MoSPDude/ZXTeensyIF1/ZXTeensyIF1/if1-2_rom.h

// if1-2.rom
// Sinclair-Interface-1-v2
#define BUILTIN_ROM_IF1_SIZE 8192
{
    0xE1, 0xFD, 0x36, 0x7C, 0x00, 0xC3, 0x00, 0x07,
    0x2A, 0x5D, 0x5C, 0xE1, 0xE5, 0xC3, 0x9A, 0x00,
    0x22, 0xBA, 0x5C, 0xE1, 0xD5, 0x18, 0x6A, 0xFF,
    0xFD, 0xCB, 0x01, 0x7E, 0xC9, 0xFF, 0xFF, 0xFF,
    0xDF, 0x28, 0x45, 0x18, 0x15, 0xFF, 0xFF, 0xFF,
    0xFD, 0xCB, 0x02, 0x9E, 0x18, 0x12, 0xFF, 0xFF,
    0xC3, 0xF7, 0x01, 0xFF, 0xFF, 0xFF, 0xFF, 0xFF,
    0xFB, 0xC9, 0xCD, 0x77, 0x00, 0xC3, 0x60, 0x02,
    0xDF, 0x28, 0x25, 0xCD, 0x77, 0x00, 0xCD, 0xB7,
    0x17, 0xFD, 0xCB, 0x7C, 0x4E, 0x28, 0x19, 0xFD,
    0xCB, 0x7C, 0x66, 0x28, 0x13, 0xFD, 0x7E, 0x00,
    0xFE, 0x14, 0x20, 0x0C, 0x21, 0x00, 0x00, 0xE5,
    0xC7, 0xFF, 0xFF, 0xFF, 0xFF, 0xFF, 0xED, 0x45,
    0x2A, 0x5D, 0x5C, 0x22, 0x5F, 0x5C, 0xED, 0x7B,
    0x3D, 0x5C, 0x21, 0xC5, 0x16, 0xE5, 0xC7, 0xFD,
    0xCB, 0x7C, 0x56, 0xC8, 0xED, 0x7B, 0x3D, 0x5C,
    0xC7, 0x5E, 0x23, 0x56, 0xED, 0x53, 0xBD, 0x5C,
    0x23, 0xE3, 0xEB, 0x21, 0x00, 0x00, 0xE5, 0x21,
    0x08, 0x00, 0xE5, 0x21, 0xB9, 0x5C, 0xE5, 0xC3,
    0x00, 0x07, 0xF5, 0x7C, 0xB5, 0x20, 0x06, 0xF1,
    0xE1, 0x2A, 0xBA, 0x5C, 0xC9, 0xD5, 0x11, 0xFE,
    0x15, 0xED, 0x52, 0xD1, 0x20, 0x0E, 0xF1, 0x21,
    0x00, 0x07, 0xE5, 0x21, 0x04, 0x00, 0x19, 0x5E,
    0x23, 0x56, 0xEB, 0xE9, 0xF7, 0x3E, 0x01, 0xD3,
    0xF7, 0x3E, 0xEE, 0xD3, 0xEF, 0xF1, 0xE1, 0xF5,
    0xD7, 0x7B, 0x00, 0x32, 0x3A, 0x5C, 0xFE, 0xFF,
    0x20, 0x17, 0xFD, 0xCB, 0x7C, 0x4E, 0x28, 0x0F,
    0xFD, 0xCB, 0x0C, 0x7E, 0x28, 0x09, 0x2A, 0x59,
    0x5C, 0x7E, 0xFE, 0xF7, 0xCA, 0x99, 0x0A, 0xE7,
    0xFF, 0xD6, 0x1B, 0xD2, 0x71, 0x1E, 0xFE, 0xF0,
    0x28, 0x09, 0xFE, 0xF3, 0x28, 0x05, 0xFE, 0xFC,
    0xC2, 0x28, 0x00, 0x2A, 0x5D, 0x5C, 0x22, 0xCB,
    0x5C, 0xF1, 0xFD, 0xCB, 0x37, 0x6E, 0xC2, 0x28,
    0x00, 0xFD, 0xCB, 0x7C, 0x46, 0xC2, 0x28, 0x00,
    0xFD, 0xCB, 0x7C, 0xC6, 0xDF, 0x20, 0x04, 0xFD,
    0x36, 0x0C, 0xFF, 0xFD, 0x46, 0x0D, 0x0E, 0x00,
    0xFD, 0xCB, 0x0C, 0x7E, 0x28, 0x0A, 0xC5, 0xD7,
    0xFB, 0x19, 0xC1, 0xD7, 0x18, 0x00, 0x18, 0x3F,
    0x2A, 0x53, 0x5C, 0x3A, 0x46, 0x5C, 0xBE, 0x30,
    0x02, 0xE7, 0x00, 0x23, 0x20, 0x06, 0x3A, 0x45,
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
},
