MoSPDude/ZXTeensyIF1/ZXTeensyIF1/mf128_rom.h

// MF128.ROM
#define BUILTIN_ROM_MF128_SIZE 8192
{
    0xC3, 0x45, 0x05, 0x14, 0x01, 0x61, 0x14, 0x00,
    0x62, 0x6F, 0x72, 0x74, 0x20, 0x4E, 0x6F, 0x20,
    0x72, 0x6F, 0x6F, 0x6D, 0x2E, 0x20, 0x43, 0x68,
    0x61, 0x6E, 0x67, 0x65, 0x20, 0x74, 0x68, 0x65,
    0x20, 0x64, 0x69, 0x73, 0x63, 0x20, 0x26, 0x20,
    0x06, 0x00, 0xE5, 0x21, 0x06, 0x20, 0x18, 0x05,
    0xC3, 0x2B, 0x62, 0x00, 0x00, 0xCB, 0xCE, 0xE1,
    0xC9, 0x14, 0x01, 0x66, 0x14, 0x00, 0x6F, 0x72,
    0x6D, 0x61, 0x74, 0x20, 0x20, 0x14, 0x01, 0x73,
    0x14, 0x00, 0x61, 0x76, 0x65, 0x06, 0x00, 0xDB,
    0x3F, 0x57, 0x72, 0x69, 0x74, 0x65, 0x20, 0x70,
    0x72, 0x6F, 0x74, 0x65, 0x63, 0x74, 0x65, 0x64,
    0x2E, 0x06, 0x00, 0xEC, 0xBC, 0xA7, 0xF5, 0xF1,
    0xC3, 0x02, 0x01, 0xC3, 0x1A, 0x05, 0xC3, 0x19,
    0x0D, 0xC3, 0x0C, 0x05, 0xC3, 0x06, 0x0D, 0xC3,
    0x06, 0x0D, 0xCD, 0xF6, 0x11, 0xD2, 0x63, 0x02,
    0x3A, 0x02, 0x20, 0xED, 0x5B, 0x00, 0x20, 0xFE,
    0x01, 0x20, 0x09, 0x21, 0xE4, 0x3F, 0x73, 0x23,
    0x72, 0xC3, 0x45, 0x05, 0xEB, 0xE9, 0x21, 0x66,
    0x64, 0x01, 0x66, 0x09, 0x11, 0x57, 0x22, 0x7E,
    0x08, 0x1A, 0x77, 0x08, 0x12, 0x23, 0x13, 0x0B,
    0x78, 0xB1, 0x20, 0xF3, 0xC9, 0xCD, 0xAE, 0x19,
    0x21, 0x17, 0x20, 0x11, 0xC0, 0x50, 0x06, 0x08,
    0xC5, 0x01, 0x40, 0x00, 0xED, 0xB0, 0x1E, 0xC0,
    0xC1, 0x10, 0xF5, 0x11, 0xC0, 0x5A, 0x01, 0x40,
    0x00, 0xED, 0xB0, 0xC9, 0xCD, 0x46, 0x08, 0xC3,
    0x0D, 0x62, 0x21, 0xF7, 0x0D, 0xC3, 0x22, 0x0D,
    0x12, 0x01, 0x20, 0x12, 0x00, 0x06, 0x06, 0x11,
    0x02, 0x10, 0x07, 0x16, 0x00, 0x00, 0xCD, 0x6D,
    0x03, 0x21, 0x00, 0xC0, 0x36, 0x00, 0xE5, 0xD1,
    0x13, 0x01, 0xFF, 0x3F, 0xED, 0xB0, 0xC9, 0xC9,
    0xC9, 0xC9, 0xC9, 0xC9, 0xC9, 0xC9, 0xC9, 0x2A,
    0x00, 0x00, 0xED, 0x73, 0xFE, 0x3F, 0x31, 0xFE,
    0x3F, 0xF5, 0xE5, 0xED, 0x57, 0xF5, 0xF3, 0xED,
    0x5F, 0xF5, 0xD5, 0xC5, 0x08, 0xF5, 0x08, 0xD9,
    0xE5, 0xD5, 0xC5, 0xD9, 0xDD, 0xE5, 0xFD, 0xE5,
    0xFD, 0x21, 0x3A, 0x5C, 0xED, 0x7B, 0xFE, 0x3F,
    0xE3, 0x31, 0xE6, 0x3F, 0xE5, 0xED, 0x7B, 0xFE,
    0x3F, 0xE3, 0x31, 0xE4, 0x3F, 0x3E, 0x71, 0x32,
    0x08, 0x20, 0xAF, 0x32, 0x06, 0x20, 0xED, 0x47,
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
},
