MoSPDude/ZXTeensyIF1/ZXTeensyIF1/z80torom.ino

// Adapted from:

// Z80toROM - Z80 snapshot to ROM Cartrdige converter
// Copyright (c) 2023, Tom Dalby
//
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
#include <stdio.h>
#include <stdint.h>
#include <stdlib.h>
#include <string.h>

//v1.0 initial release
//v1.1 attempt to fix issue with earlier Spectrums
//v1.2 refactoring, bug fix on loader introduced in v1.1, handle pc in stack, stack in screen & ability to force final loader to screen
//v1.3 changed output header format and routine to create names from filename to match compressrom

// E00 - invalid option
// E01 - input file not Z80 or SNA snapshot
// E02 - cannot open snapshot for read
// E03 - cannot create output file
// E04 - unsupported Z80 snapshot
// E05 - special memory page mode, +3/+2A only so not supported
// E06 - not enough memory
// E07 - input file read error, issue with Z80/SNA snapshot
// E11 - cannot compress as won't fit into ROM

typedef union {
    uint32_t rrrr; //byte number
    uint8_t r[4]; //split number into 4 8bit bytes in case of overflow
} rrrr;

    // loader machine code
#define romReg_brd 34   // Border Colour
#define romReg_ffff 87  // restore 0xffff
#define romReg_fffd 121 // last OUT to 0xfffd
#define romReg_out 127  // last OUT to 0x7ffd
#define romReg_sp 147   // SP
#define romReg_jp 152   // Hard coded to 0x3FF4, as z80FinalLoader location
#define romReg_ay 154   // 16 AY Registers (39 - 54)
#define romReg_bca 170  // BC'
#define romReg_dea 172  // DE'
#define romReg_hla 174  // HL'
#define romReg_ix 176   // IX
#define romReg_iy 178   // IY
#define romReg_afa 180  // AF' (F',A')
#define romReg_hl 182   // HL
#define romReg_de 184   // DE
#define romReg_bc 186   // BC
#define romReg_f 188    // F
#define romReg_r 189    // R
#define romReg_bnks 229 // 128k banks if needed
#define romReg_len SNA_LOADER_FIRST_SIZE
const uint8_t PROGMEM z80FirstLoader[romReg_len] = {
    0xf3,0x3e,0x80,0xed,0x47,0xaf,0xd3,0xfe,0x21,0x00,0x58,0x77,0x54,0x1e,0x01,0x01,
    0xff,0x02,0xed,0xb0,0x21,0xbe,0x00,0x16,0x60,0x01,0x2e,0x00,0xed,0xb0,0xc3,0x00,
    0x60,0x3e,0x00,0xd3,0xfe,0x31,0x00,0x00,0x21,0xec,0x00,0x11,0x00,0x40,0x43,0x18,
    0x0d,0x00,0x00,0x00,0x00,0x00,0x00,0x00,0xed,0x4d,0x3c,0x4f,0xed,0xb0,0x7e,0x23,
    0xfe,0x80,0x28,0x12,0x38,0xf4,0xd6,0x7e,0x4e,0x23,0xe5,0x62,0x6b,0xed,0x42,0x2b,
    0x4f,0xed,0xb0,0xe1,0x18,0xe8,0x21,0x00,0x00,0xe5,0x31,0x9a,0x00,0x01,0xfd,0xff,
    0xaf,0xe1,0xed,0x79,0x3c,0x06,0xbf,0xed,0x69,0x06,0xff,0xed,0x79,0x3c,0x06,0xbf,
    0xed,0x61,0xfe,0x10,0x06,0xff,0x20,0xe9,0x3e,0x00,0xed,0x79,0x06,0x7f,0x3e,0x30,
    0xed,0x79,0xd9,0xc1,0xd1,0xe1,0xd9,0xdd,0xe1,0xfd,0xe1,0x08,0xf1,0x08,0xe1,0xd1,
    0xc1,0xf1,0x31,0x00,0x00,0xed,0x4f,0xc3,0xf4,0x3f,0x00,0x00,0x00,0x00,0x00,0x00,
    0x00,0xff,0x00,0x00,0x00,0x00,0x00,0x00,0xbf,0x00,0x00,0xff,0x00,0xff,0x1a,0xf8,
    0xf1,0xe3,0x3a,0x5c,0x8a,0x00,0x4c,0x10,0xcc,0x43,0x00,0x00,0x00,0x02,0x3a,0xff,
    0x3f,0xd9,0x11,0x00,0x80,0x01,0x00,0x40,0x61,0x6c,0xed,0xb0,0xd9,0x21,0x27,0x60,
    0x01,0xfd,0x7f,0x7e,0x23,0xb7,0xca,0x21,0x00,0xed,0x79,0xd9,0x44,0x65,0x16,0xc0,
    0xed,0xb0,0xd9,0x18,0xee,0x30,0x00,0x13,0x14,0x16,0x17,0x00 };

#define pcReg_i 1
#define pcReg_im 5    // Interupt Mode
#define pcReg_a 7     // A
#define pcReg_ei 8    // DI or EI
#define pcReg_jp 10    // PC
#define pcReg_len SNA_LOADER_FINAL_SIZE
const uint8_t PROGMEM z80FinalLoader[pcReg_len] = {
    0x3e,0x3f,0xed,0x47,0xed,0x5e,0x3e,0x00,0xfb,0xc3,0xb7,0xd9 };

// ---------------------------------------------------------------------------
// dcz80 - decompress z80 snapshot routine
// ---------------------------------------------------------------------------
uint16_t dcz80(File file, uint8_t* out, uint16_t size) {
    uint16_t i = 0, k, j;
    uint8_t c;
    while (i < size) {
        file.read(&c, 1);
        if (c == 0xed) { // is it 0xed [0]
            file.read(&c, 1);
            if (c == 0xed) { // is 2nd 0xed then a sequence
                file.read(&c, 1);
                j = c;
                file.read(&c, 1);
                for (k = 0; k < j; k++) out[i++] = c;
            }
            else {
                out[i++] = 0xed;
                file.seek(-1, SeekCur); // back one
            }
        }
        else {
            out[i++] = c; // just copy
        }
    }
    return i;
}

//
// ---------------------------------------------------------------------------
// simplelz - very simple lz with 256byte backward look
//   x=128+ then copy sequence from x-offset from next byte offset
//   x=0-127 then copy literal x+1 times
//   minimum sequence size 2
// ---------------------------------------------------------------------------
uint32_t simplelz(uint8_t* fload, uint8_t* store, uint32_t filesize) {
    uint32_t i;
    uint8_t* store_p, * store_c;

    int litsize = 1;
    uint32_t repsize, offset, repmax, offmax;
    store_c = store;
    store_p = store_c + 1;
    //
    i = 0;
    offmax = 0;
    *store_p++ = fload[i++];
    do {
        // scan for sequence
        repmax = 2;
        if (i > 255) offset = i - 256; else offset = 0;
        do {
            repsize = 0;
            while ((i + repsize < filesize) && (repsize < 129) &&
                (fload[offset + repsize] == fload[i + repsize]))
            {
                repsize++;
            }
            if (repsize > repmax) {
                repmax = repsize;
                offmax = i - offset;
            }
            offset++;
        } while ((offset < i) && (repmax < 129));
        if (repmax > 2) {
            if (litsize > 0) {
                *store_c = litsize - 1;
                store_c = store_p++;
                litsize = 0;
            }
            *store_p++ = offmax - 1; //1-256 -> 0-255
            *store_c = repmax + 126;
            store_c = store_p++;
            i += repmax;
        }
        else {
            litsize++;
            *store_p++ = fload[i++];
            if (litsize > 127) {
                *store_c = litsize - 1;
                store_c = store_p++;
                litsize = 0;
            }
        }
    } while (i < filesize);
    if (litsize > 0) {
        *store_c = litsize - 1;
        store_c = store_p++;
    }
    *store_c = 128;    // end marker
    return store_p - store;
}

uint8_t convertZ80toROM(File file, uint8_t* store, uint8_t* main, bool snap)
{
    // Transfer the first and final loader directly into the ROM
    int i = 0;
    uint8_t* const romReg = store;
    uint8_t* const pcReg = &(store[(ROM_PAGE_SIZE - pcReg_len)]); // 0x3FF4
    memcpy(romReg, z80FirstLoader, romReg_len);
    memcpy(pcReg, z80FinalLoader, pcReg_len);

    // Start to load the snapshot
    file.seek(0, SeekEnd); // jump to the end of the file to get the length
    int filesize = file.position(); // get the file size
    file.seek(0, SeekSet);
    //
    int otek = 0;
    uint8_t compressed = 0;
    rrrr addlen;
    addlen.rrrr = 0; // z80 only, 0 indicates v1, 23 for v2 otherwise v3
    uint8_t c;
    //read is sna, compressed=0, addlen.rrrr=0, otek=0
    if (snap) {
        if (filesize < 49179) return 0;
        if (filesize >= 131103) otek = 1; // 128k snapshot
        //    $00  I    Interrupt register
        pcReg[pcReg_i] = file.read();
        //    $01  HL'
        romReg[romReg_hla] = file.read();
        romReg[romReg_hla + 1] = file.read();
        //    $03  DE'
        romReg[romReg_dea] = file.read();
        romReg[romReg_dea + 1] = file.read();
        // check this is a SNA snapshot
        if (pcReg[pcReg_i] == 'M' && romReg[romReg_hla] == 'V' &&
            romReg[romReg_hla + 1] == ' ' && romReg[romReg_dea] == '-') return 0;
        if (pcReg[pcReg_i] == 'Z' && romReg[romReg_hla] == 'X' &&
            romReg[romReg_hla + 1] == '8' && romReg[romReg_dea] == '2') return 0;
        //    $05  BC'
        romReg[romReg_bca] = file.read();
        romReg[romReg_bca + 1] = file.read();
        //    $07  F'
        romReg[romReg_afa] = file.read();
        //    $08  A'
        romReg[romReg_afa + 1] = file.read();
        //    $09  HL
        romReg[romReg_hl] = file.read();
        romReg[romReg_hl + 1] = file.read();
        //    $0B  DE
        romReg[romReg_de] = file.read();
        romReg[romReg_de + 1] = file.read();
        //    $0D  BC
        romReg[romReg_bc] = file.read();
        romReg[romReg_bc + 1] = file.read();
        //    $0F  IY
        romReg[romReg_iy] = file.read();
        romReg[romReg_iy + 1] = file.read();
        //    $11  IX
        romReg[romReg_ix] = file.read();
        romReg[romReg_ix + 1] = file.read();
        //    $13  0 for DI otherwise EI
        c = file.read();
        if (c == 0) pcReg[pcReg_ei] = 0xf3;    //di
        else pcReg[pcReg_ei] = 0xfb;    //ei
        //    $14  R
        romReg[romReg_r] = file.read();
        //    $15  F
        romReg[romReg_f] = file.read();
        //    $16  A
        pcReg[pcReg_a] = file.read();
        //    $17  SP
        romReg[romReg_sp] = file.read();
        romReg[romReg_sp + 1] = file.read();
        if (!otek) {
            if (romReg[romReg_sp] > 253) {
                romReg[romReg_sp + 1]++;
                romReg[romReg_sp] -= 254;
            }
            else {
                romReg[romReg_sp] += 2;
            }
        }
        // $19  Interrupt mode IM(0, 1 or 2)
        c = file.read() & 3;
        if (c == 0) pcReg[pcReg_im] = 0x46; //im 0
        else if (c == 1) pcReg[pcReg_im] = 0x56; //im 1
        else pcReg[pcReg_im] = 0x5e; //im 2
        //    $1A  Border colour
        c = file.read() & 7;
        romReg[romReg_brd] = c + 0x30;
    }
    // read z80
    else {
        //read in z80 starting with header
        //    0       1       A register
        pcReg[pcReg_a] = file.read();
        //    1       1       F register
        romReg[romReg_f] = file.read();
        //    2       2       BC register pair(LSB, i.e. C first)
        romReg[romReg_bc] = file.read();
        romReg[romReg_bc + 1] = file.read();
        //    4       2       HL register pair
        romReg[romReg_hl] = file.read();
        romReg[romReg_hl + 1] = file.read();
        //    6       2       Program counter (if zero then version 2 or 3 snapshot)
        pcReg[pcReg_jp] = file.read();
        pcReg[pcReg_jp + 1] = file.read();
        //    8       2       Stack pointer
        romReg[romReg_sp] = file.read();
        romReg[romReg_sp + 1] = file.read();
        //    10      1       Interrupt register
        pcReg[pcReg_i] = file.read();
        //    11      1       Refresh register (Bit 7 is not significant!)
        c = file.read();
        romReg[romReg_r] = c;
        //    12      1       Bit 0: Bit 7 of r register; Bit 1-3: Border colour; Bit 4=1: SamROM; Bit 5=1:v1 Compressed; Bit 6-7: N/A
        c = file.read();
        compressed = (c & 32) >> 5;    // 1 compressed, 0 not
        if (c & 1 || c > 127) {
            romReg[romReg_r] = romReg[romReg_r] | 128;    // r high bit set
        }
        else {
            romReg[romReg_r] = romReg[romReg_r] & 127;    //r high bit reset
        }
        romReg[romReg_brd] = ((c & 14) >> 1) + 0x30; //border
        //    13      2       DE register pair
        romReg[romReg_de] = file.read();
        romReg[romReg_de + 1] = file.read();
        //    15      2       BC' register pair
        romReg[romReg_bca] = file.read();
        romReg[romReg_bca + 1] = file.read();
        //    17      2       DE' register pair
        romReg[romReg_dea] = file.read();
        romReg[romReg_dea + 1] = file.read();
        //    19      2       HL' register pair
        romReg[romReg_hla] = file.read();
        romReg[romReg_hla + 1] = file.read();
        //    21      1       A' register
        romReg[romReg_afa + 1] = file.read();
        //    22      1       F' register
        romReg[romReg_afa] = file.read();
        //    23      2       IY register (Again LSB first)
        romReg[romReg_iy] = file.read();
        romReg[romReg_iy + 1] = file.read();
        //    25      2       IX register
        romReg[romReg_ix] = file.read();
        romReg[romReg_ix + 1] = file.read();
        //    27      1       Interrupt flipflop, 0 = DI, otherwise EI
        c = file.read();
        if (c == 0) pcReg[pcReg_ei] = 0xf3;    //di
        else pcReg[pcReg_ei] = 0xfb;    //ei
        //    28      1       IFF2 [IGNORED]
        c = file.read();
        //    29      1       Bit 0-1: IM(0, 1 or 2); Bit 2-7: N/A
        c = file.read() & 3;
        if (c == 0) pcReg[pcReg_im] = 0x46; //im 0
        else if (c == 1) pcReg[pcReg_im] = 0x56; //im 1
        else pcReg[pcReg_im] = 0x5e; //im 2
        // version 2 & 3 only
        if (pcReg[pcReg_jp] == 0 && pcReg[pcReg_jp + 1] == 0) {
            //  30      2       Length of additional header block
            addlen.r[0] = file.read();
            addlen.r[1] = file.read();
            //  32      2       Program counter
            pcReg[pcReg_jp] = file.read();
            pcReg[pcReg_jp + 1] = file.read();
            //    34      1       Hardware mode standard 0-6 (2 is SamRAM), 7 +3, 8 +3 & 10 not supported, 11 Didatik, 12 +2, 13 +2A
            c = file.read();
            if (c == 2 || c == 10 || c == 11 || c > 13) return 0;
            if (addlen.rrrr == 23 && c > 2) otek = 1; // v2 & c>2 then 128k, if v3 then c>3 is 128k
            else if (c > 3) otek = 1;
            //    35      1       If in 128 mode, contains last OUT to 0x7ffd
            c = file.read();
            if (otek) romReg[romReg_out] = c;
            //    36      1       Contains 0xff if Interface I rom paged [SKIPPED]
            //    37      1       Hardware Modify Byte [SKIPPED]
            file.seek(2, SeekCur);
            //    38      1       Last OUT to port 0xfffd (soundchip register number)
            //    39      16      Contents of the sound chip registers
            romReg[romReg_fffd] = file.read();    // last out to $fffd (38)
            for (i = 0; i < 16; i++) romReg[romReg_ay + i] = file.read(); // ay registers (39-54)
            // following is only in v3 snapshots
            //    55      2       Low T state counter [SKIPPED]
            //    57      1       Hi T state counter [SKIPPED]
            //    58      1       Flag byte used by Spectator (QL spec.emulator) [SKIPPED]
            //    59      1       0xff if MGT Rom paged [SKIPPED]
            //    60      1       0xff if Multiface Rom paged. Should always be 0. [SKIPPED]
            //    61      1       0xff if 0 - 8191 is ROM, 0 if RAM [SKIPPED]
            //    62      1       0xff if 8192 - 16383 is ROM, 0 if RAM [SKIPPED]
            //    63      10      5 x keyboard mappings for user defined joystick [SKIPPED]
            //    73      10      5 x ASCII word : keys corresponding to mappings above [SKIPPED]
            //    83      1       MGT type : 0 = Disciple + Epson, 1 = Disciple + HP, 16 = Plus D [SKIPPED]
            //    84      1       Disciple inhibit button status : 0 = out, 0ff = in [SKIPPED]
            //    85      1       Disciple inhibit flag : 0 = rom pageable, 0ff = not [SKIPPED]
            if (addlen.rrrr > 23) file.seek(31, SeekCur);
            // only if version 3 & 55 additional length
            //    86      1       Last OUT to port 0x1ffd, ignored as only applicable on +3/+2A machines [SKIPPED]
            if (addlen.rrrr == 55)     if ((file.read() & 1) == 1) return 0;
        }
    }
    // space for decompression of z80
    // 8 * 16384 = 131072bytes
    //     0-49152 - Pages 5,2 & 0 (main memory)
    // *128k only - 49152-65536: Page 1; 65536-81920: Page 3; 81920-98304: Page 4; 98304-114688: Page 6; 114688-131072: Page 7
    /*int fullsize = 49152;
    if (otek) {
        fullsize = 131072;
    }
    //
    uint8_t* main;
    if ((main = (uint8_t*)malloc(fullsize * sizeof(uint8_t))) == NULL)
    {
        return 0;
    }*/
    //
    rrrr len;
    len.rrrr = 0;
    //set-up bank locations
    int bank[11], bankend;
    for (i = 0; i < 11; i++) bank[i] = 99; //default
    if (otek) {
        bank[3] = 32768; //page 0
        bank[4] = 49152; //page 1
        bank[5] = 16384; //page 2
        bank[6] = 65536; //page 3
        bank[7] = 81920; //page 4
        bank[8] = 0; //page 5
        bank[9] = 98304; //page 6
        bank[10] = 114688; //page 7
        bankend = 8;
    }
    else {
        bank[4] = 16384; //page 2
        bank[5] = 32768; //page 0
        bank[8] = 0; //page 5
        bankend = 3;
    }
    if (addlen.rrrr == 0) { // SNA or version 1 z80 snapshot & 48k only
        if (!compressed) {
            if (file.read(main, 49152) != 49152)
            {
                return 0;
            }
            // sort out pc for SNA
            if (snap) {
                uint32_t stackpos = romReg[romReg_sp] + romReg[romReg_sp + 1] * 256;
                if (stackpos == 0) stackpos = 65536;
                pcReg[pcReg_jp] = main[stackpos - 16384 - 2];
                pcReg[pcReg_jp + 1] = main[stackpos - 16384 - 1];
            }
        }
        else {
            if (dcz80(file, main, 49152) != 49152)
            {
                return 0;
            }
        }
        if (otek) {
            // PC
            pcReg[pcReg_jp] = file.read();
            pcReg[pcReg_jp + 1] = file.read();
            // last out to 0x7ffd
            romReg[romReg_out] = file.read();
            // TD-DOS
            if (file.read() != 0)
            {
                return 0;
            }
            uint32_t pagelayout[7];
            for (i = 0; i < 7; i++) pagelayout[i] = 99;
            pagelayout[0] = romReg[romReg_out] & 7;
            //
            if (pagelayout[0] == 0) {
                pagelayout[0] = 32768;
                pagelayout[1] = 49152;
                pagelayout[2] = 65536;
                pagelayout[3] = 81920;
                pagelayout[4] = 98304;
                pagelayout[5] = 114688;
            }
            else if (pagelayout[0] == 1) {
                pagelayout[0] = 49152;
                pagelayout[1] = 32768;
                pagelayout[2] = 65536;
                pagelayout[3] = 81920;
                pagelayout[4] = 98304;
                pagelayout[5] = 114688;
            }
            else if (pagelayout[0] == 2) {
                pagelayout[0] = 16384;
                pagelayout[1] = 32768;
                pagelayout[2] = 49152;
                pagelayout[3] = 65536;
                pagelayout[4] = 81920;
                pagelayout[5] = 98304;
                pagelayout[6] = 114688;
            }
            else if (pagelayout[0] == 3) {
                pagelayout[0] = 65536;
                pagelayout[1] = 32768;
                pagelayout[2] = 49152;
                pagelayout[3] = 81920;
                pagelayout[4] = 98304;
                pagelayout[5] = 114688;
            }
            else if (pagelayout[0] == 4) {
                pagelayout[0] = 81920;
                pagelayout[1] = 32768;
                pagelayout[2] = 49152;
                pagelayout[3] = 65536;
                pagelayout[4] = 98304;
                pagelayout[5] = 114688;
            }
            else if (pagelayout[0] == 5) {
                pagelayout[0] = 0;
                pagelayout[1] = 32768;
                pagelayout[2] = 49152;
                pagelayout[3] = 65536;
                pagelayout[4] = 81920;
                pagelayout[5] = 98304;
                pagelayout[6] = 114688;
            }
            else if (pagelayout[0] == 6) {
                pagelayout[0] = 98304;
                pagelayout[1] = 32768;
                pagelayout[2] = 49152;
                pagelayout[3] = 65536;
                pagelayout[4] = 81920;
                pagelayout[5] = 114688;
            }
            else {
                pagelayout[0] = 114688;
                pagelayout[1] = 32768;
                pagelayout[2] = 49152;
                pagelayout[3] = 65536;
                pagelayout[4] = 81920;
                pagelayout[5] = 98304;
            }
            if (pagelayout[0] != 32768) {
                for (i = 0; i < 16384; i++) main[pagelayout[0] + i] = main[32768 + i]; //copy 0->?
            }
            for (i = 1; i < 7; i++) {
                if (pagelayout[i] != 99) {
                    if (file.read(&main[pagelayout[i]], 16384) != 16384)
                    {
                        return 0;
                    }
                }
            }
        }
    }
    // version 2 & 3
    else {
        //        Byte    Length  Description
        //        -------------------------- -
        //        0       2       Length of compressed data(without this 3 - byte header)
        //                        If length = 0xffff, data is 16384 bytes longand not compressed
        //        2       1       Page number of block
        // for 48k snapshots the order is:
        //        0 48k ROM, 1, IF1/PLUSD/DISCIPLE ROM, 4 page 2, 5 page 0, 8 page 5, 11 MF ROM
        //        only 4, 5 & 8 are valid for this usage, all others are just ignored
        // for 128k snapshots the order is:
        //        0 ROM, 1 ROM, 3 Page 0....10 page 7, 11 MF ROM.
        // all pages are saved and there is no end marker
        do {
            len.r[0] = file.read();
            len.r[1] = file.read();
            c = file.read();
            if (bank[c] != 99) {
                if (len.rrrr == 65535) {
                    if (file.read(&main[bank[c]], 16384) != 16384)
                    {
                        return 0;
                    }
                }
                else {
                    if (dcz80(file, &main[bank[c]], 16384) != 16384)
                    {
                        return 0;
                    }
                }
            }
            bankend--;
        } while (bankend);
    }

    // Compress Bank 5 to check for room for loaders
    rrrr cmsize;
    cmsize.rrrr = simplelz(main, &store[romReg_len], ROM_PAGE_SIZE);
    if (cmsize.rrrr >= SNA_LOADER_BANK_5_SIZE)
    {
        return 0;
    }

    // Correct R by the 9 cycles to perform "LD R, A"
    // NOTE: Bits 6:0 are the counter, preserve bit 7 as read
    uint8_t regMSB = romReg[romReg_r] & 0x80;
    romReg[romReg_r] = (romReg[romReg_r] - 9) & 0x7F;
    romReg[romReg_r] |= regMSB;

    // Update first loader with number of banks
    uint8_t banks = 3;
    if (otek) {
        banks = 8;
        romReg[romReg_bnks] = 0x10;
        romReg[romReg_bnks + 1] = 0x11;
    }
    uint32_t size = banks * ROM_PAGE_SIZE;
    romReg[romReg_ffff] = main[size - 2];
    romReg[romReg_ffff + 1] = main[size - 1];

    // Store remaining banks
    for (i = 1; i < banks; i++) {
        memcpy(&(store[(ROM_PAGE_SIZE * i)]), &(main[(ROM_PAGE_SIZE * i)]), ROM_PAGE_SIZE);
    }
    return banks;
}
