MoSPDude/ZXTeensyIF1/ZXTeensyIF1/lib765/765fdc.c

/* 765: Library to emulate the uPD765a floppy controller (aka Intel 8272)

    Copyright (C) 2000, 2008  John Elliott <jce@seasip.demon.co.uk>

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
*/
#include "765i.h"

/* The number of bytes in the 32 possible FDC commands */

static int bytes_in_cmd[32] = { 1,  /* 0 = none */
                                1,  /* 1 = none */
                                9,  /* 2 = READ TRACK */
                                3,  /* 3 = SPECIFY */
                                2,  /* 4 = SENSE DRIVE STATUS */
                                9,  /* 5 = WRITE DATA */
                                9,  /* 6 = READ DATA */
                                2,  /* 7 = RECALIBRATE */
                                1,  /* 8 = SENSE INTERRUPT STATUS */
                                9,  /* 9 = WRITE DELETED DATA */
                                2,  /* 10 = READ SECTOR ID */
                                1,  /* 11 = none */
                                9,  /* 12 = READ DELETED DATA */
                                6,  /* 13 = FORMAT A TRACK */
                                1,  /* 14 = none */
                                3,  /* 15 = SEEK */
                                1,  /* 16 = none */
                                9,  /* 17 = SCAN EQUAL */
                                1,  /* 18 = none */
                                1,  /* 19 = none */
                                1,  /* 20 = none */
                                1,  /* 21 = none */
                                1,  /* 22 = none */
                                1,  /* 23 = none */
                                1,  /* 24 = none */
                                9,  /* 25 = SCAN LOW OR EQUAL */
                                1,  /* 26 = none */
                                1,  /* 27 = none */
                                1,  /* 28 = none */
                                1,  /* 29 = none */
                                9,  /* 30 = SCAN HIGH OR EQUAL */
                                1   /* 31 = none */
                              };

/**********************************************************************
 *                        FDC IMPLEMENTATION                          *
 **********************************************************************/


/* Partial reset (done by pulling bit 2 of the DOR low) */
static void fdc_part_reset(FDC_765 *self)
{
	int n;

	self->fdc_mainstat       = 0x80;	/* Ready */
	self->fdc_st0            = 0;
	self->fdc_st1            = 0;
	self->fdc_st2            = 0;
	self->fdc_st3	         = 0;
	self->fdc_curunit        = 0;
	self->fdc_curhead        = 0;
	self->fdc_cmd_id         = -1;
	self->fdc_cmd_len        = 0;
	self->fdc_cmd_pos        = 0;
	self->fdc_exec_len       = 0;
	self->fdc_exec_pos       = 0;
	self->fdc_result_len     = 0;
	self->fdc_result_pos     = 0;
	memset(self->fdc_cmd_buf,   0, sizeof(self->fdc_cmd_buf));
	memset(self->fdc_exec_buf,  0, sizeof(self->fdc_exec_buf));
	memset(self->fdc_result_buf,0, sizeof(self->fdc_result_buf));
/* Reset any changelines */
	for (n = 0; n < 4; n++)
	{
		if (self->fdc_drive[n]) self->fdc_drive[n]->fd_changed = 0;
	}
}


/* Initialise / reset the FDC */
void fdc_reset(FDC_765 *self)
{
	self->fdc_interrupting   = 0;
	self->fdc_specify[0]     = self->fdc_specify[1] = 0;
	self->fdc_lastidread     = 0;
	self->fdc_terminal_count = 0;
	self->fdc_isr            = NULL;
	self->fdc_isr_countdown  = 0L;
	self->fdc_dor		 = -1;	/* Not using the DOR at all */
	memset(self->fdc_drive,     0, sizeof(self->fdc_drive));
	fdc_part_reset(self);
}

static void fdc_dorcheck(FDC_765 *self)
{
	int n;

	/* v0.1.0: Check if the DOR is forcing us to select a different
	 * drive. */
	if (self->fdc_dor < 0)
		for (n = 0; n < 4; n++) self->fdc_dor_drive[n] = self->fdc_drive[n];
	else	for (n = 0; n < 4; n++) self->fdc_dor_drive[n] = self->fdc_drive[self->fdc_dor & 3];
}



/* Update the ST3 register based on a drive's status */
static void fdc_get_st3(FDC_765 *self)
{
	FLOPPY_DRIVE *fd = self->fdc_dor_drive[self->fdc_curunit];
	fdc_byte value = 0;

	/* 0.3.4: Check this, it could be null! */
	if (fd->fd_vtable->fdv_drive_status)
	{
		value = (*fd->fd_vtable->fdv_drive_status)(fd);
	}
	value &= 0xF8;
	value |= (self->fdc_curhead ? 4 : 0);
	value |= (self->fdc_curunit & 3);
	self->fdc_st3 = value;
}

/* Check if a drive is ready */
int fdc_isready(FDC_765 *self, FLOPPY_DRIVE *fd)
{
        int rdy = fd_isready(fd);

        if (!rdy) {self->fdc_st3 &= 0xDF; return 0; }
        self->fdc_st3 |= 0x20;
        return 1;
}


/* Convert an error from the fd_* routines to a value in the status registers */
static void fdc_xlt_error(FDC_765 *self, fd_err_t error)
{
	//fdc_dprintf(4, "FDC: Error from drive: %d\n", error);
        switch(error)
        {
                case FD_E_NOTRDY: self->fdc_st0 |= 0x48; break;
		case FD_E_SEEKFAIL:
				  self->fdc_st0 |= 0x40;
				  self->fdc_st2 |= 0x02; break;
                case FD_E_NOADDR: self->fdc_st0 |= 0x40;
                                  self->fdc_st2 |= 0x01; break;
                case FD_E_NODATA: self->fdc_st0 |= 0x40;
                                  self->fdc_st1 |= 0x04; break;
		case FD_E_DATAERR:
				  self->fdc_st1 |= 0x20;
				  self->fdc_st2 |= 0x20; break;
                case FD_E_NOSECTOR:
                                  self->fdc_st0 |= 0x40;
                                  self->fdc_st1 |= 0x82; break;
                case FD_E_READONLY:
				  self->fdc_st0 |= 0x40;
				  self->fdc_st1 |= 0x02; break;
        }

}

/* Fill out 7 result bytes
 * XXX Bytes 2,3,4,5 should change the way the real FDC does it. */
static void fdc_results_7(FDC_765 *self)
{
	self->fdc_result_buf[0] = self->fdc_st0;	/* 3 status registers */
        self->fdc_result_buf[1] = self->fdc_st1;
        self->fdc_result_buf[2] = self->fdc_st2;
        self->fdc_result_buf[3] = self->fdc_cmd_buf[2];	/* C, H, R, N */
        self->fdc_result_buf[4] = self->fdc_cmd_buf[3];
        self->fdc_result_buf[5] = self->fdc_cmd_buf[4];
        self->fdc_result_buf[6] = self->fdc_cmd_buf[5];
	self->fdc_mainstat = 0xD0;	/* Ready to return results */
}
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
